damianevans/project-busker/hardware/ADC_Board/ADC_Board-B_Cu.pdf

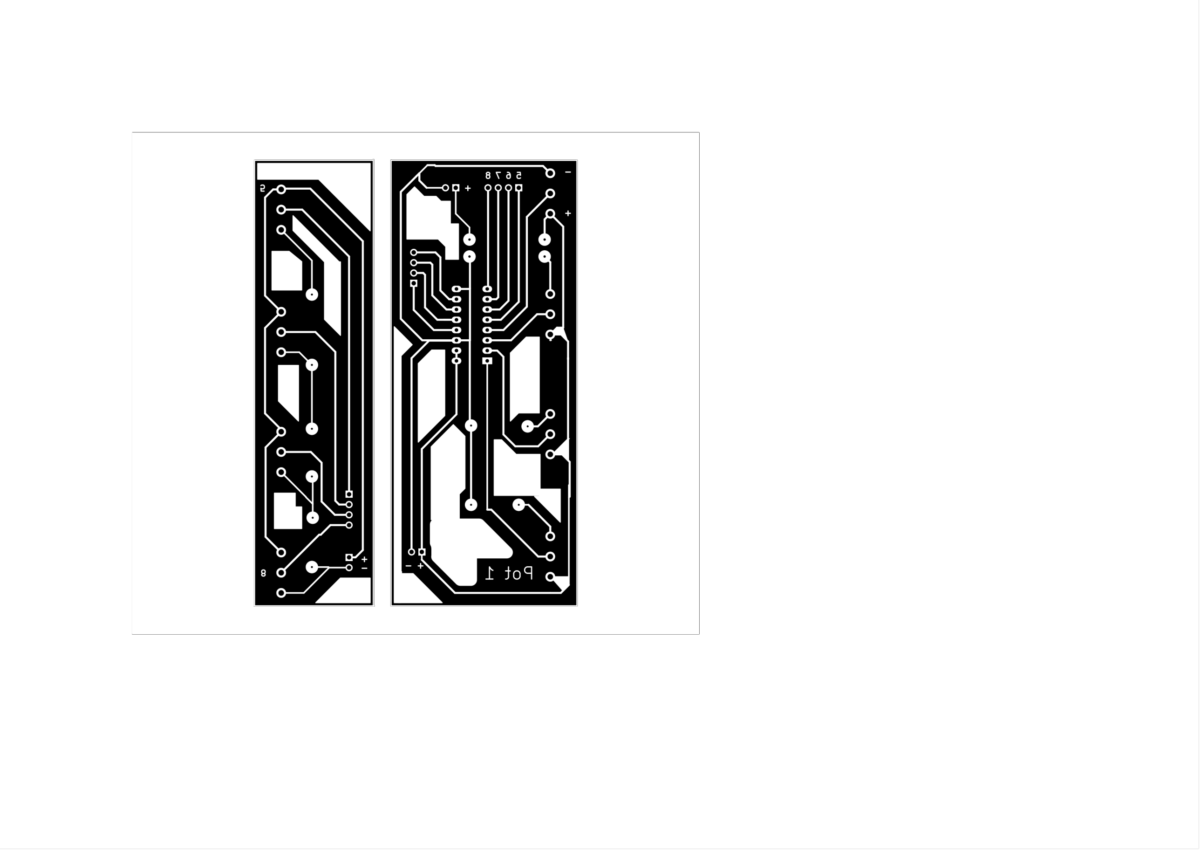
[picture p5: page 1]
