damianevans/project-busker/hardware/pre-ampv3/guitar-pre-ampv3-B_Cu.pdf

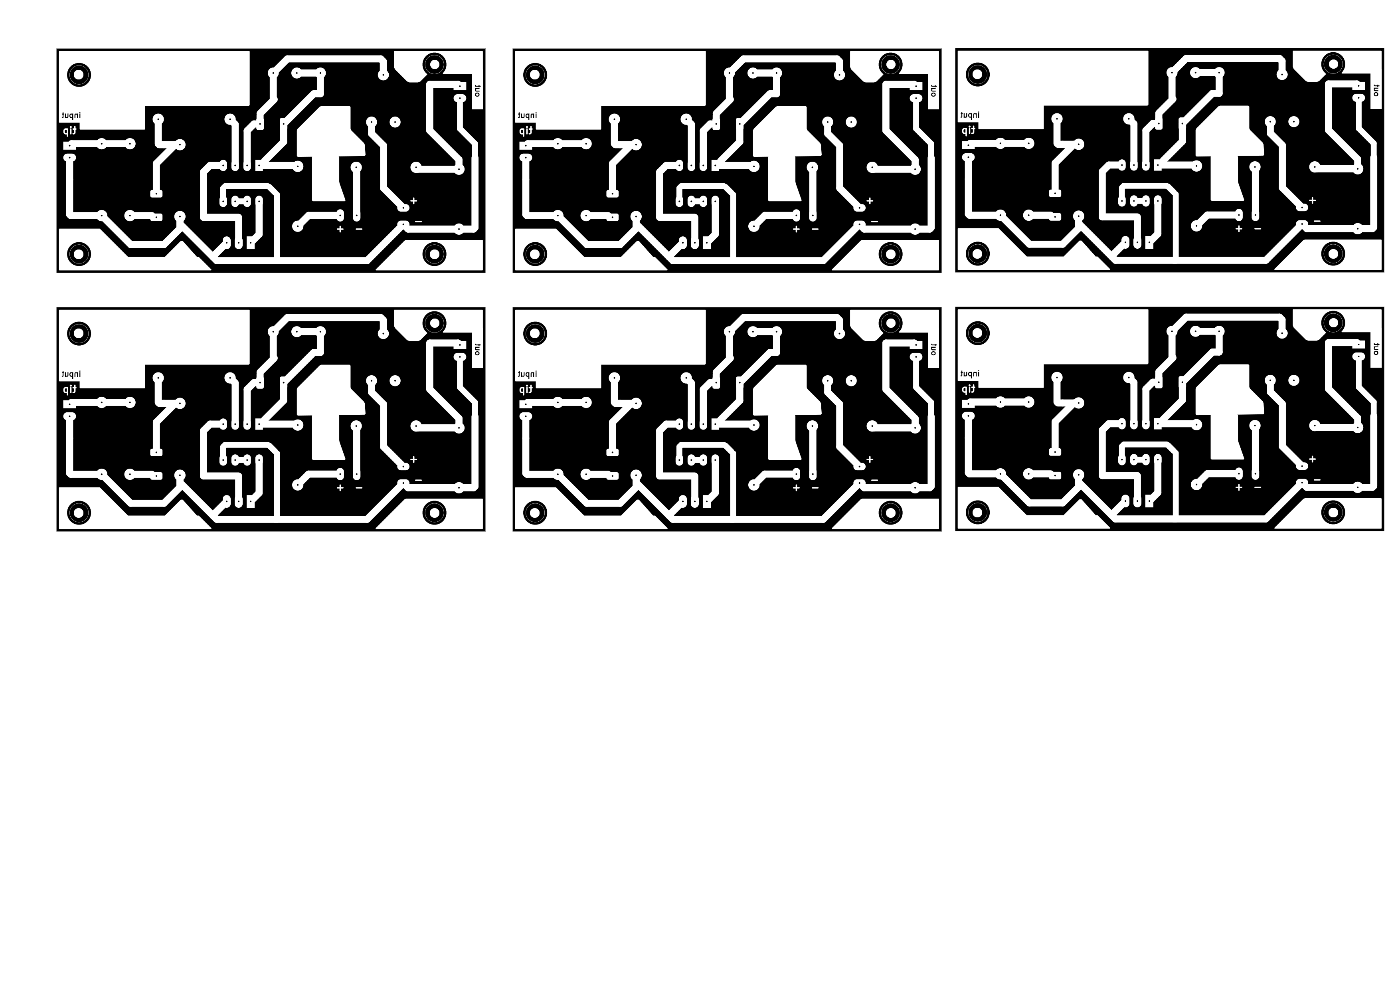
[picture p6: page 1]
