damianevans/project-busker/hardware/vu_leds/vu_leds/vu_leds-B_Cu.pdf

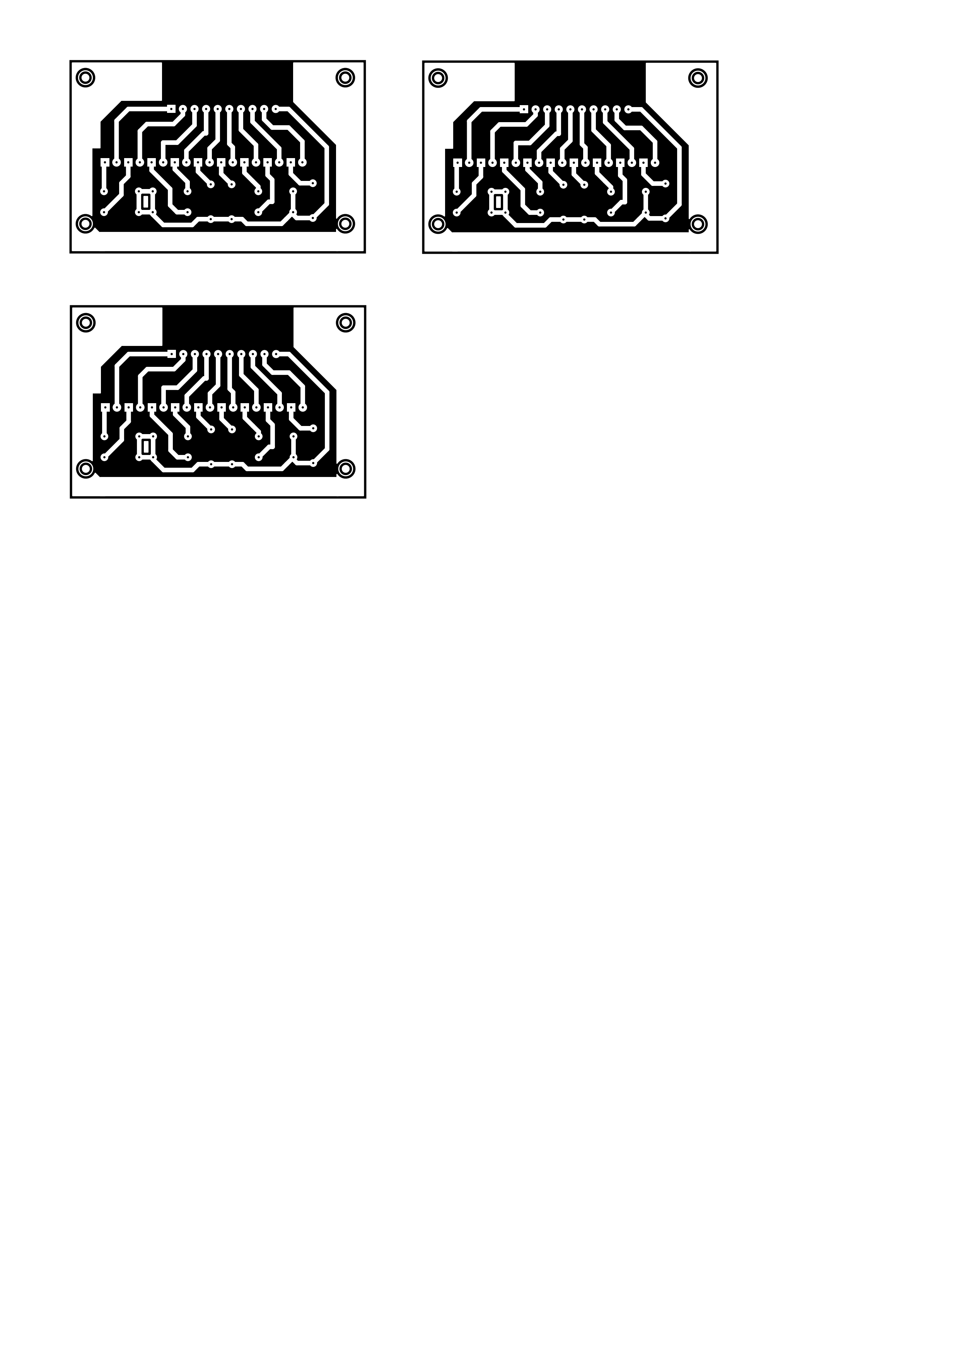
[picture p7: page 1]
