damianevans/project-busker/hardware/pre-ampv3/guitar-pre-ampv3-F_Cu.pdf

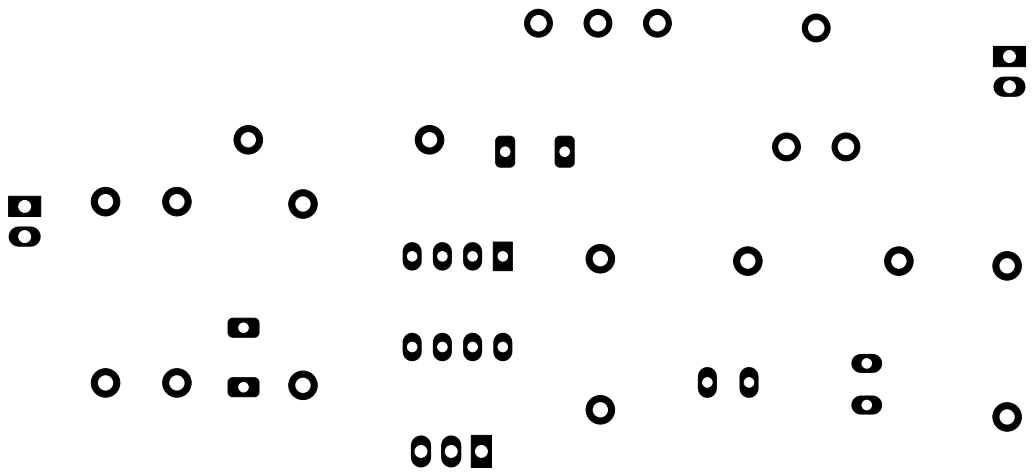
[picture p14: page 1]
